AntonDudDm/Hydraulic-manipulator/CAD/Шприц/шприц сборка.SLDASM

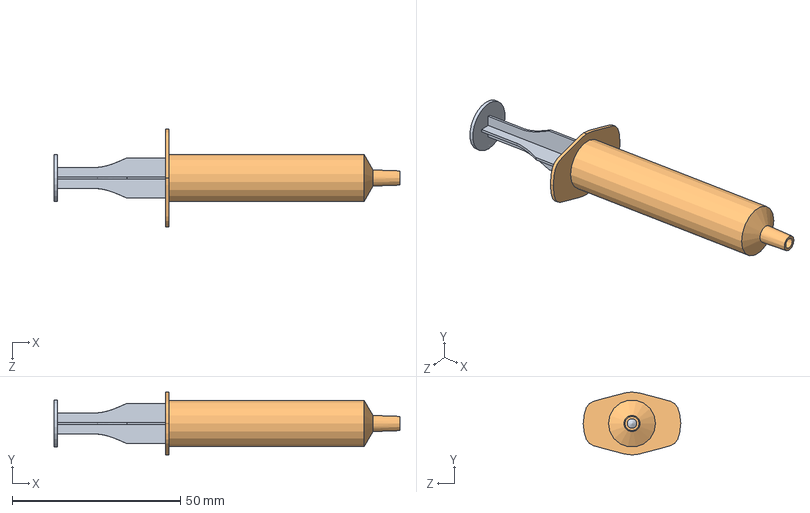
[picture p15: CAD file, 2025-12-12]
CAD/Шприц/шприц сборка.SLDASM
102.8 x 18.7 x 29.0 mm
шприц корпус 5 мм
шприц шток 5 мм
