AntonDudDm/Hydraulic-manipulator/CAD/Захват и мотор №4/Шарнир наклона захвата/Шарнир захвата.SLDPRT

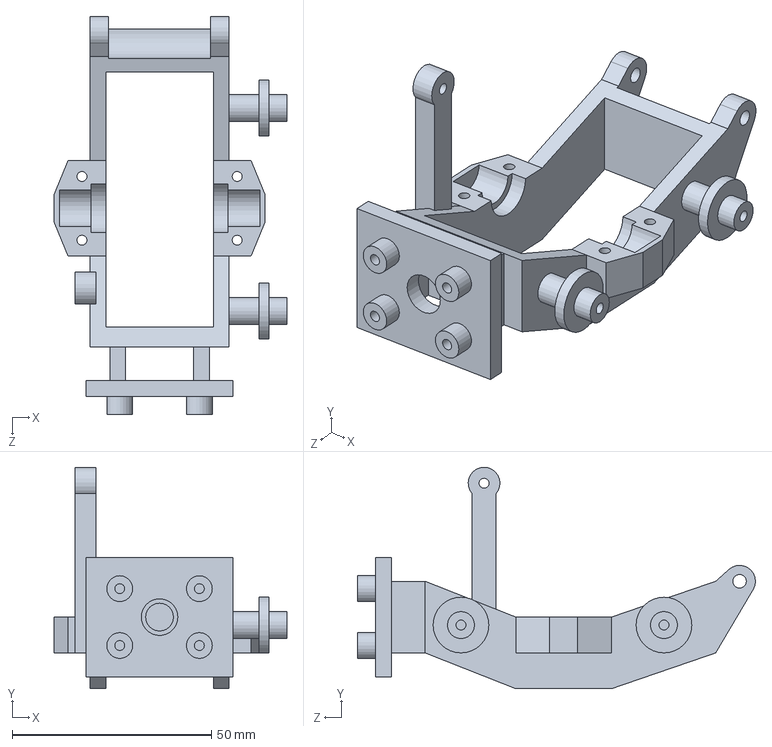
[picture p22: CAD file, 2025-12-12]
CAD/Захват и мотор №4/Шарнир наклона захвата/Шарнир захвата.SLDPRT
58.5 x 55.6 x 100.0 mm
