AntonDudDm/Hydraulic-manipulator/CAD/Крепежи оси №2/Крепеж подрельсовые к мотору №2 верхняя.SLDPRT

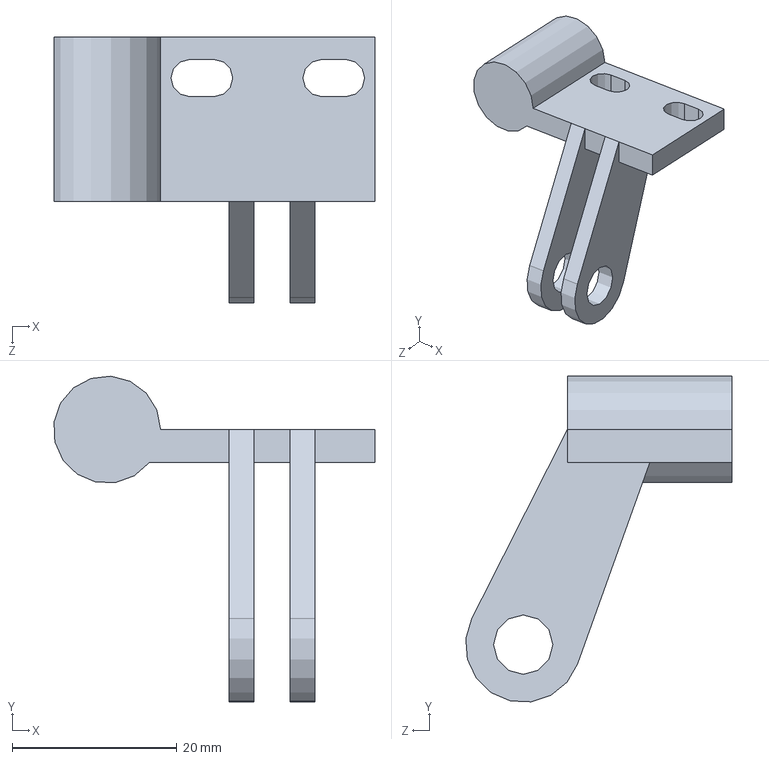
[picture p23: CAD file, 2025-12-12]
CAD/Крепежи оси №2/Крепеж подрельсовые к мотору №2 верхняя.SLDPRT
38.9 x 39.5 x 32.3 mm
