AntonDudDm/Hydraulic-manipulator/CAD/Мотор №1/Детали/Тяга с шайбой_1 ось.SLDPRT

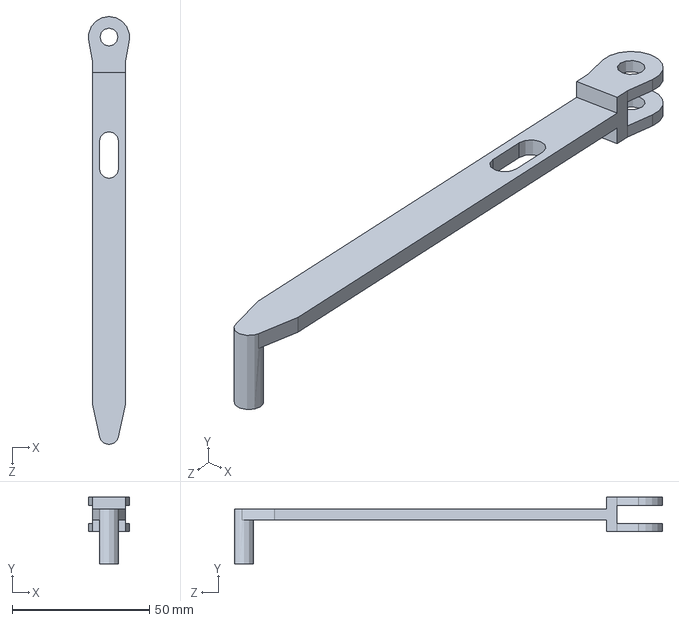
[picture p24: CAD file, 2025-12-12]
CAD/Мотор №1/Детали/Тяга с шайбой_1 ось.SLDPRT
14.8 x 24.2 x 156.0 mm
