AntonDudDm/Hydraulic-manipulator/CAD/Мотор №2/Детали/Заглушка на ось_на клей.SLDPRT

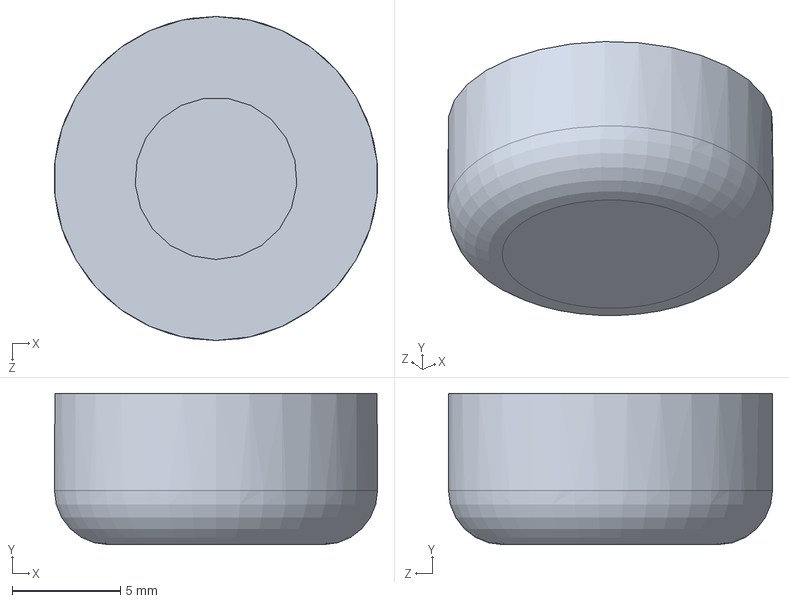
[picture p25: CAD file, 2025-12-12]
CAD/Мотор №2/Детали/Заглушка на ось_на клей.SLDPRT
15.0 x 7.00 x 15.0 mm
