AntonDudDm/Hydraulic-manipulator/CAD/Мотор №3/Детали  мотор №3/Крепёж штока мотора мотор №3.SLDPRT

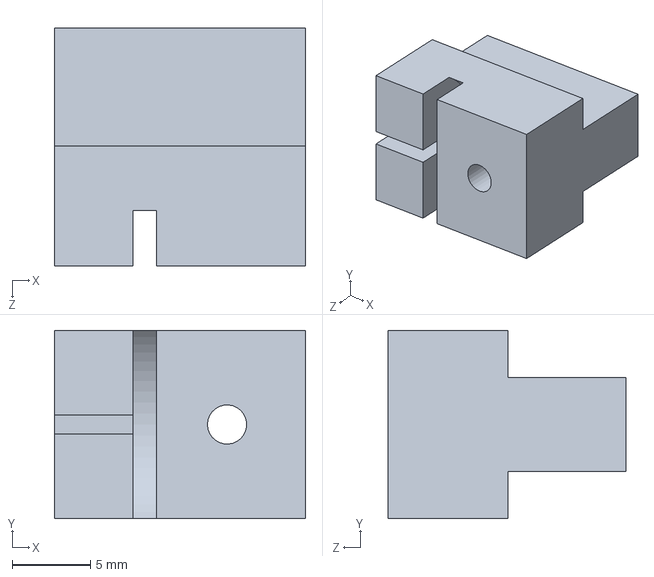
[picture p26: CAD file, 2025-12-12]
CAD/Мотор №3/Детали мотор №3/Крепёж штока мотора мотор №3.SLDPRT
16.0 x 12.0 x 15.1 mm
