AntonDudDm/Hydraulic-manipulator/CAD/Шприц/шприц корпус 5 мм.SLDPRT

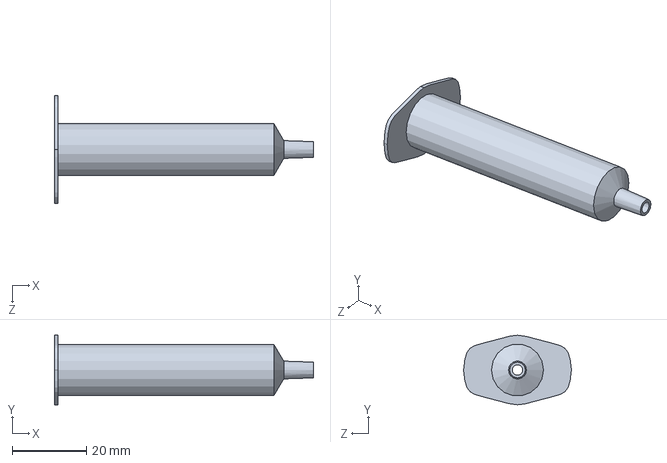
[picture p27: CAD file, 2025-12-12]
CAD/Шприц/шприц корпус 5 мм.SLDPRT
69.7 x 18.7 x 29.0 mm
