AntonDudDm/Hydraulic-manipulator/CAD/Гидронасос/Детали гидронасос/Крепёж к платформе.SLDPRT

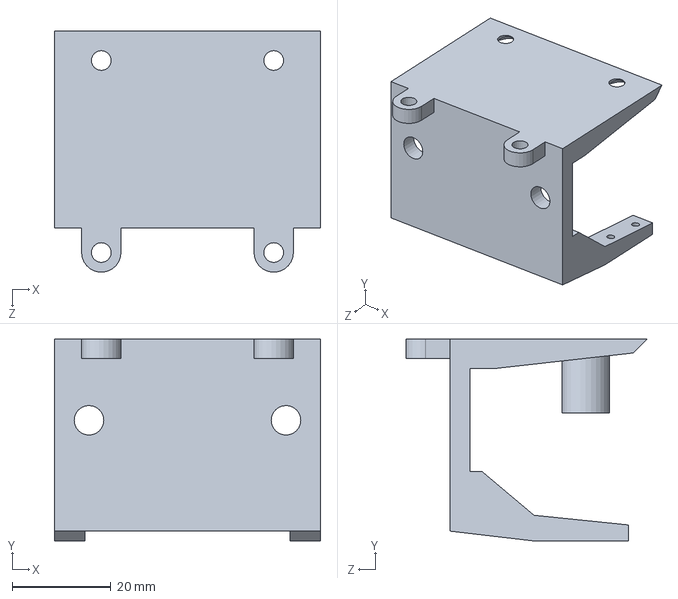
[picture p28: CAD file, 2025-12-12]
CAD/Гидронасос/Детали гидронасос/Крепёж к платформе.SLDPRT
54.0 x 41.0 x 49.0 mm
