AntonDudDm/Hydraulic-manipulator/CAD/Гидронасос/Сервопривод/Прицепная шайба.SLDPRT

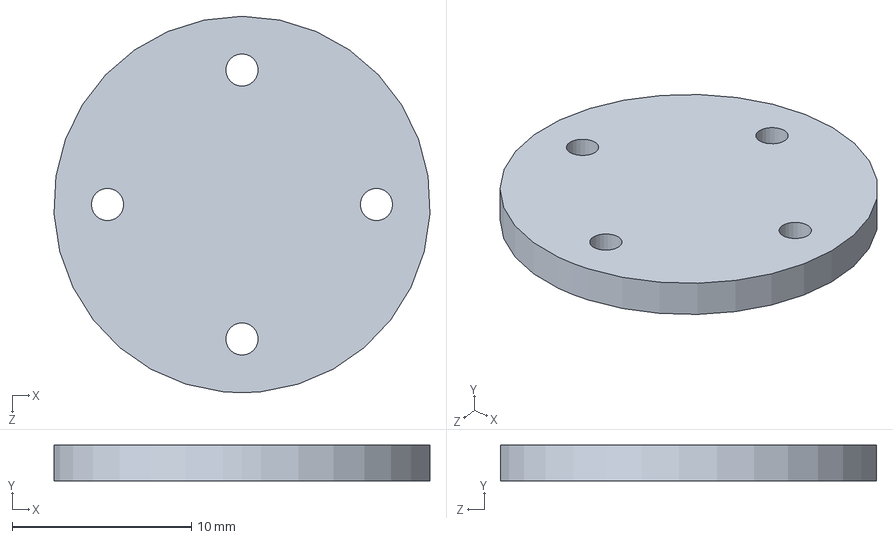
[picture p29: CAD file, 2025-12-12]
CAD/Гидронасос/Сервопривод/Прицепная шайба.SLDPRT
21.0 x 2.00 x 21.0 mm
