AntonDudDm/Hydraulic-manipulator/CAD/Детали и крепления сборки/Крепёж рельсовых.SLDPRT

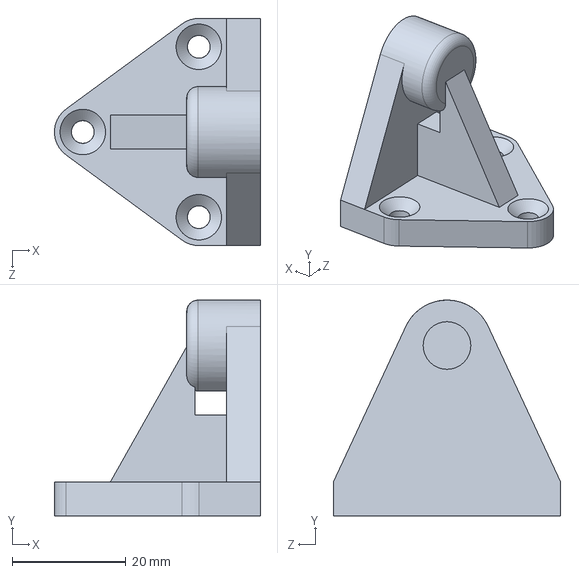
[picture p30: CAD file, 2025-12-12]
CAD/Детали и крепления сборки/Крепёж рельсовых.SLDPRT
36.3 x 38.0 x 40.0 mm
