AntonDudDm/Hydraulic-manipulator/CAD/Детали под электронику/Джойстик/Коробка под джойстик Верх.SLDPRT

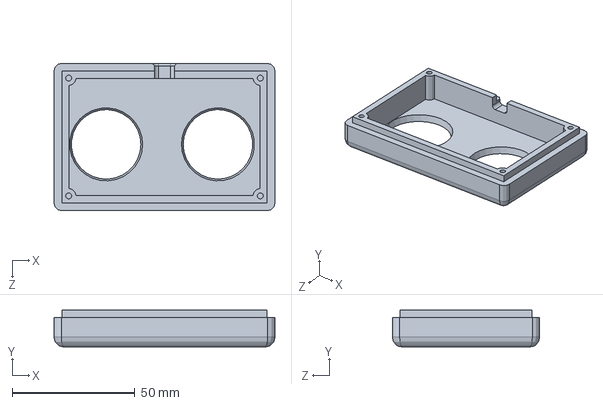
[picture p31: CAD file, 2025-12-12]
CAD/Детали под электронику/Джойстик/Коробка под джойстик Верх.SLDPRT
90.0 x 15.0 x 60.0 mm
