AntonDudDm/Hydraulic-manipulator/CAD/Детали под электронику/крепеж ардуино UNO.SLDPRT

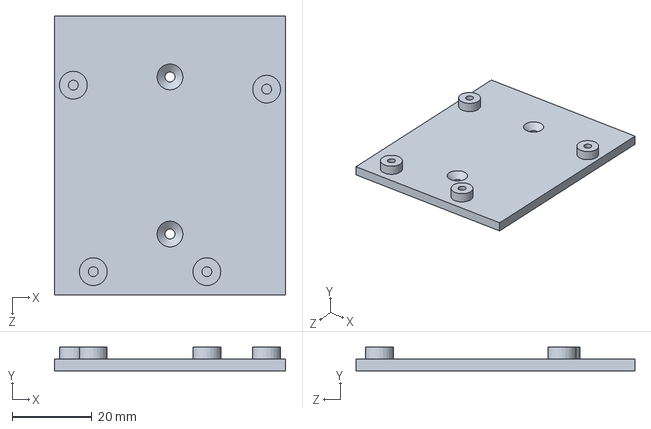
[picture p32: CAD file, 2025-12-12]
CAD/Детали под электронику/крепеж ардуино UNO.SLDPRT
58.0 x 6.00 x 70.0 mm
