AntonDudDm/Hydraulic-manipulator/CAD/Захват и мотор №4/Захват/Детали фаланги/3 фаланга.SLDPRT

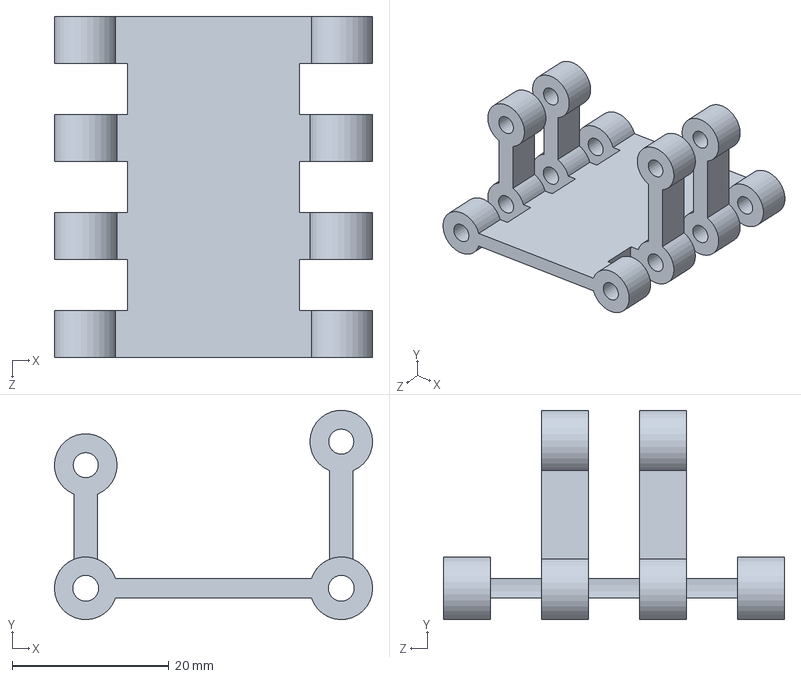
[picture p33: CAD file, 2025-12-12]
CAD/Захват и мотор №4/Захват/Детали фаланги/3 фаланга.SLDPRT
40.6 x 26.7 x 43.5 mm
