AntonDudDm/Hydraulic-manipulator/CAD/Захват и мотор №4/Планетарная передача/Детали планетарка/Сателлит.SLDPRT

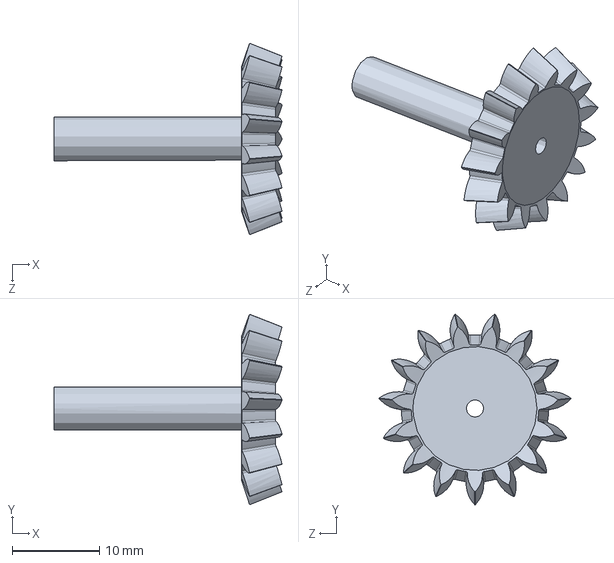
[picture p34: CAD file, 2025-12-12]
CAD/Захват и мотор №4/Планетарная передача/Детали планетарка/Сателлит.SLDPRT
26.2 x 21.9 x 22.0 mm
