AntonDudDm/Hydraulic-manipulator/CAD/Захват и мотор №4/Шток к мотору №3.SLDPRT

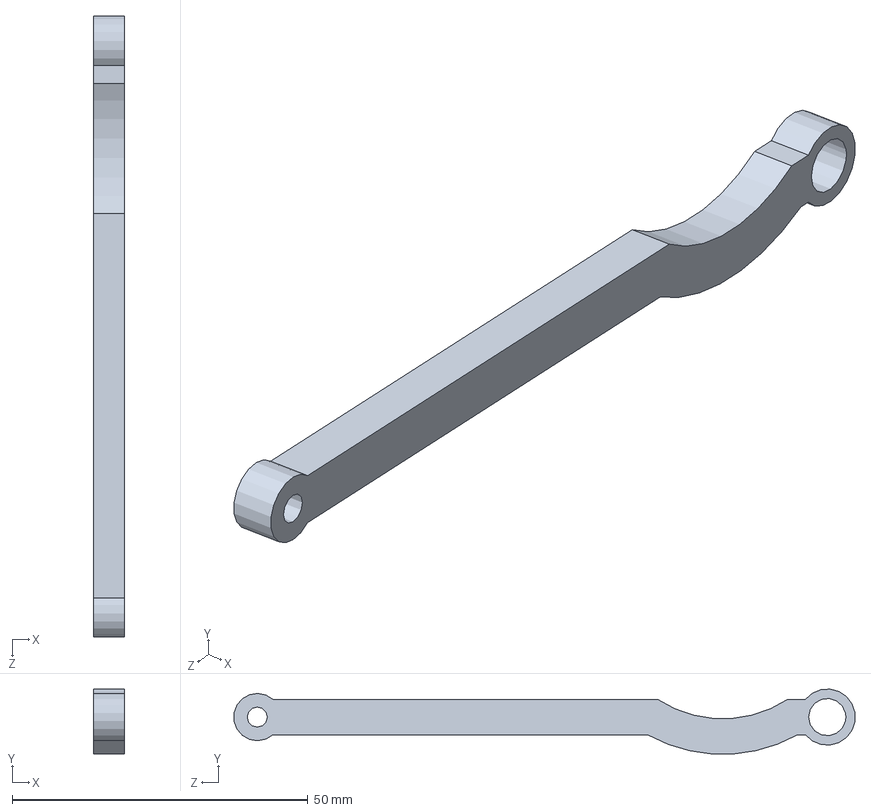
[picture p35: CAD file, 2025-12-12]
CAD/Захват и мотор №4/Шток к мотору №3.SLDPRT
5.20 x 11.0 x 105.0 mm
