AntonDudDm/Hydraulic-manipulator/CAD/Крепежи оси №2/Крепеж подрельсовые к мотору №2 нижняя.SLDPRT

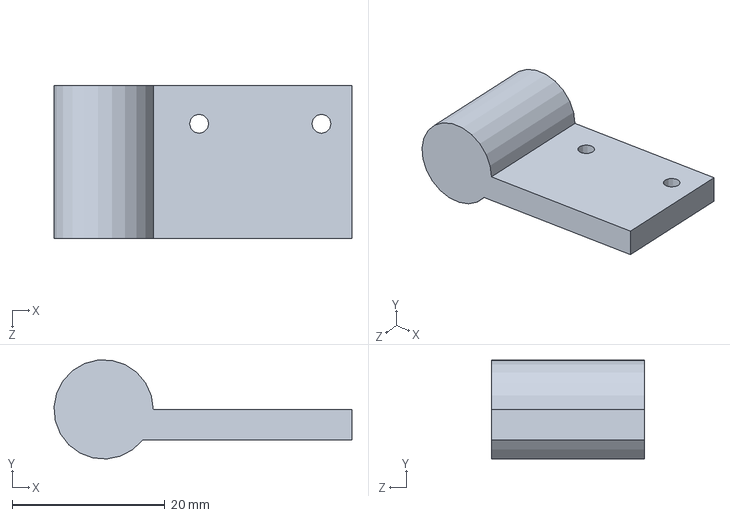
[picture p36: CAD file, 2025-12-12]
CAD/Крепежи оси №2/Крепеж подрельсовые к мотору №2 нижняя.SLDPRT
39.0 x 12.9 x 20.0 mm
