AntonDudDm/Hydraulic-manipulator/CAD/Мотор №1/Детали/Крепёж под шприц_1 ось.SLDPRT

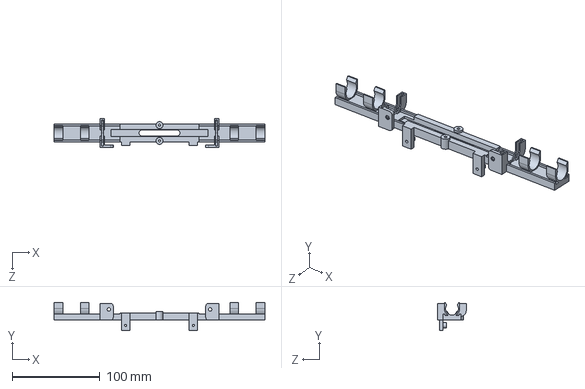
[picture p37: CAD file, 2025-12-12]
CAD/Мотор №1/Детали/Крепёж под шприц_1 ось.SLDPRT
240.0 x 32.2 x 33.0 mm
