AntonDudDm/Hydraulic-manipulator/CAD/Шприц/шприц шток 5 мм.SLDPRT

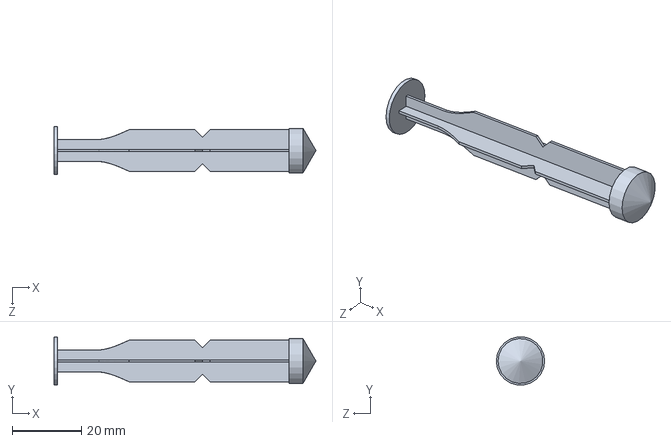
[picture p38: CAD file, 2025-12-12]
CAD/Шприц/шприц шток 5 мм.SLDPRT
75.8 x 13.9 x 14.0 mm
