AntonDudDm/Hydraulic-manipulator/CAD/Гидронасос/Детали гидронасос/Крепёж под шприц, нагнетатель.SLDPRT

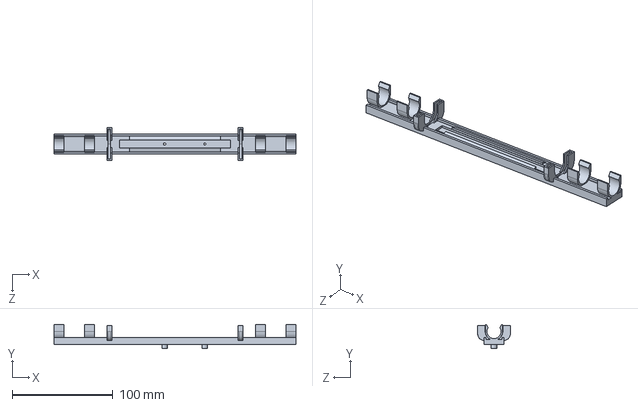
[picture p39: CAD file, 2025-12-12]
CAD/Гидронасос/Детали гидронасос/Крепёж под шприц, нагнетатель.SLDPRT
240.0 x 24.2 x 33.0 mm
