AntonDudDm/Hydraulic-manipulator/CAD/Гидронасос/Сервопривод/Корпус сервопривода.SLDPRT

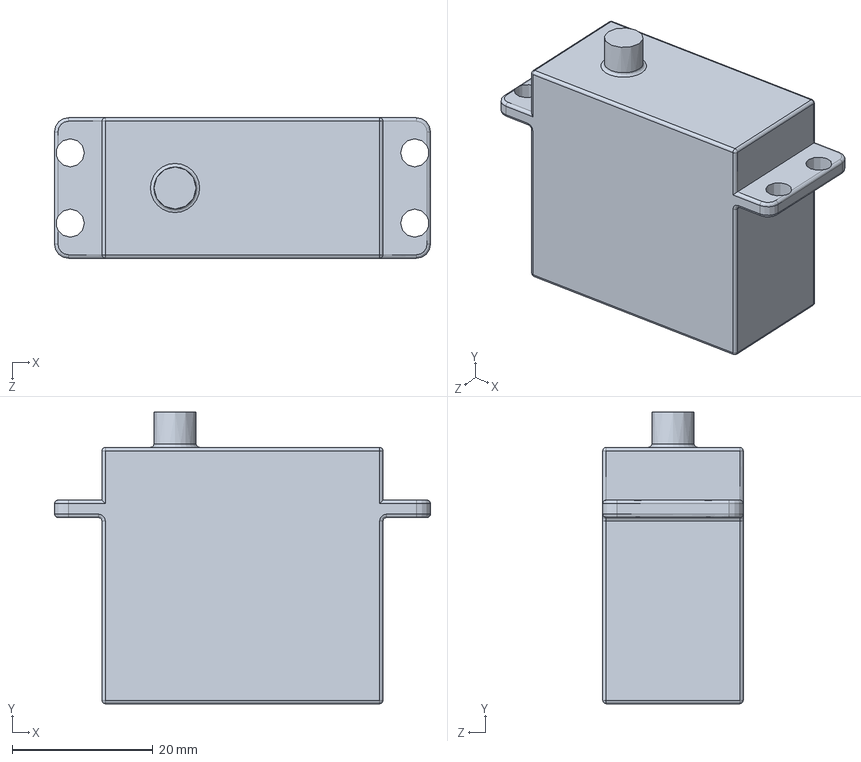
[picture p40: CAD file, 2025-12-12]
CAD/Гидронасос/Сервопривод/Корпус сервопривода.SLDPRT
53.5 x 41.5 x 20.0 mm
