AntonDudDm/Hydraulic-manipulator/CAD/Детали и крепления сборки/стол фанера 18.мм..SLDPRT

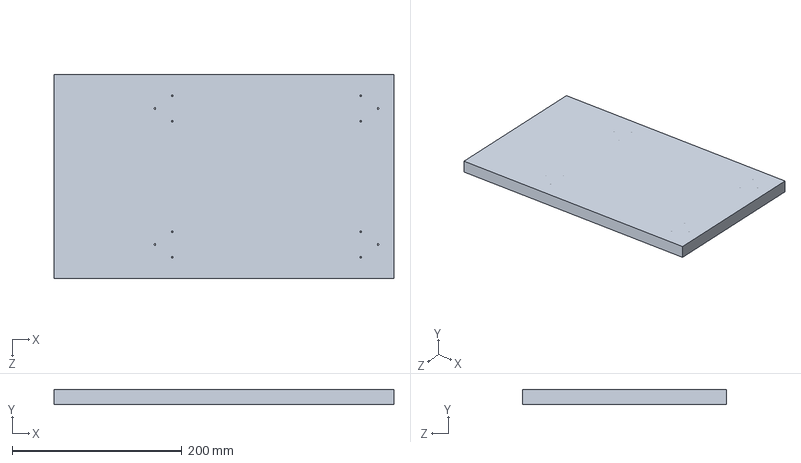
[picture p41: CAD file, 2025-12-12]
CAD/Детали и крепления сборки/стол фанера 18.мм..SLDPRT
400.0 x 18.0 x 240.0 mm
