AntonDudDm/Hydraulic-manipulator/CAD/Детали под электронику/Джойстик/Коробка под джойстик Низ.SLDPRT

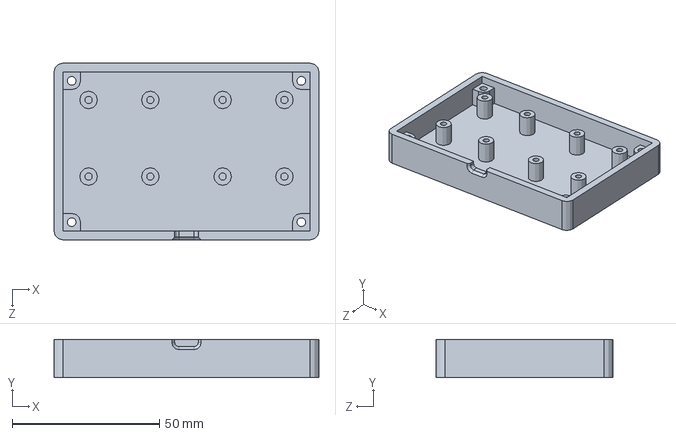
[picture p42: CAD file, 2025-12-12]
CAD/Детали под электронику/Джойстик/Коробка под джойстик Низ.SLDPRT
90.0 x 13.0 x 60.0 mm
