AntonDudDm/Hydraulic-manipulator/CAD/Детали под электронику/Крепеж проводов.SLDPRT

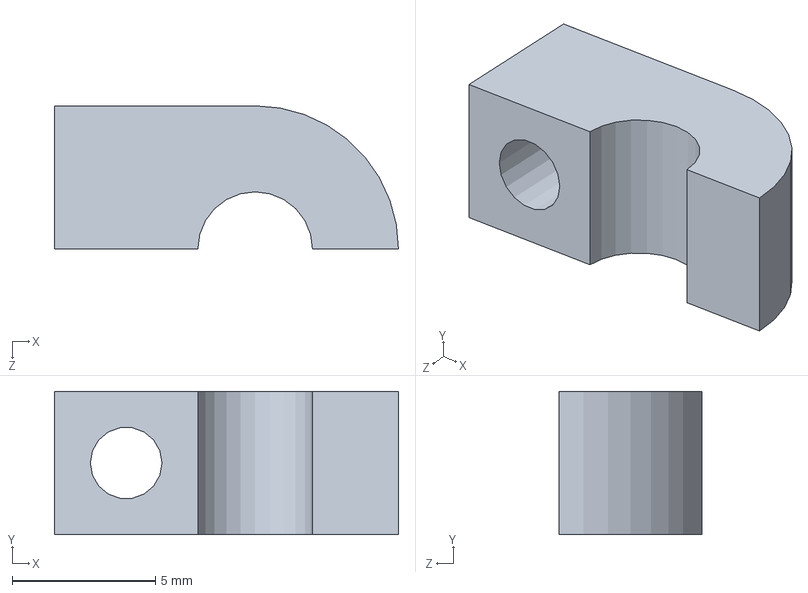
[picture p43: CAD file, 2025-12-12]
CAD/Детали под электронику/Крепеж проводов.SLDPRT
12.0 x 5.00 x 5.00 mm
