AntonDudDm/Hydraulic-manipulator/CAD/Захват и мотор №4/Захват/Детали фаланги/тяга 1 фаланга.SLDPRT

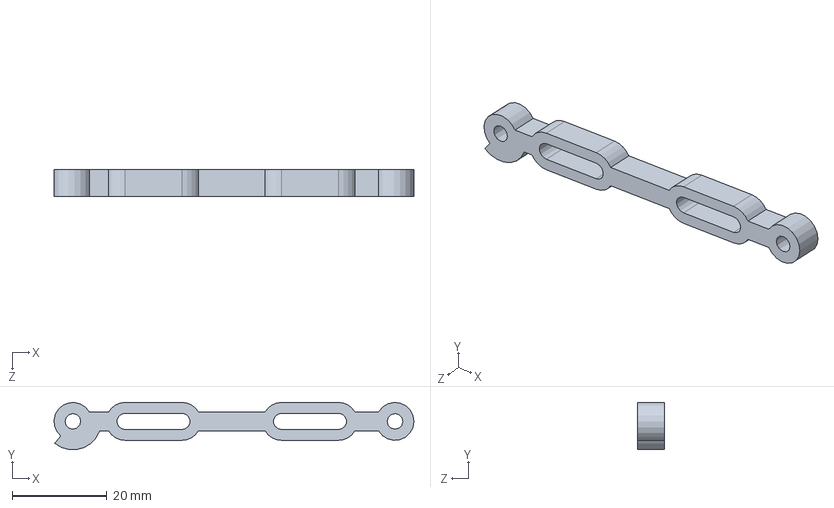
[picture p44: CAD file, 2025-12-12]
CAD/Захват и мотор №4/Захват/Детали фаланги/тяга 1 фаланга.SLDPRT
75.9 x 9.95 x 5.60 mm
