AntonDudDm/Hydraulic-manipulator/CAD/Крепежи оси №2/Крепеж подрельсовые оси №2 к каретке каркаса.SLDPRT

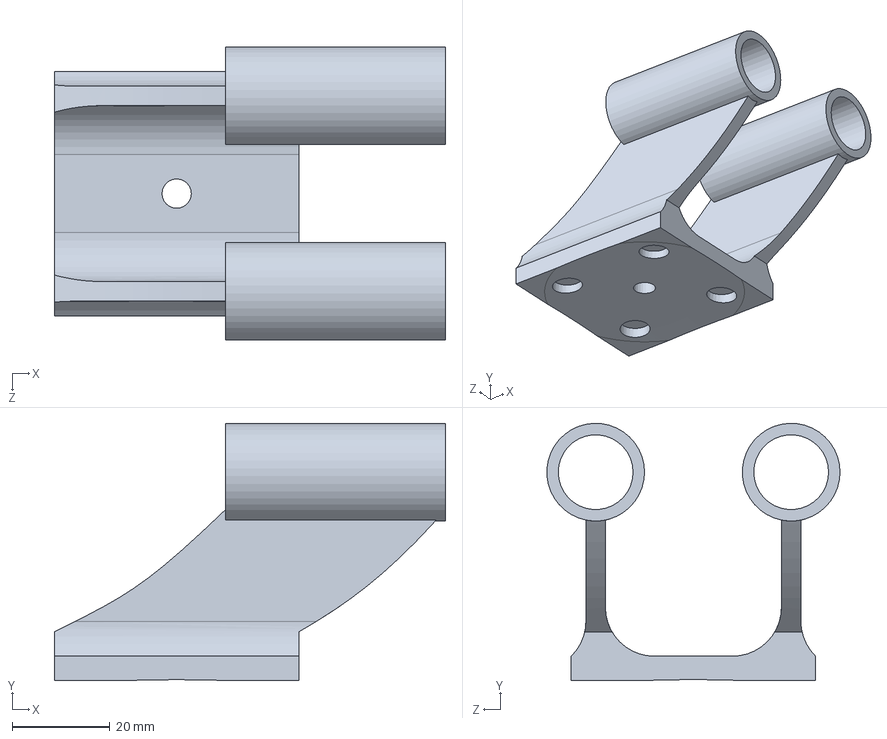
[picture p45: CAD file, 2025-12-12]
CAD/Крепежи оси №2/Крепеж подрельсовые оси №2 к каретке каркаса.SLDPRT
80.0 x 52.6 x 60.0 mm
