AntonDudDm/Hydraulic-manipulator/CAD/Мотор №1/Детали/Крепёж штока_1 ось.SLDPRT

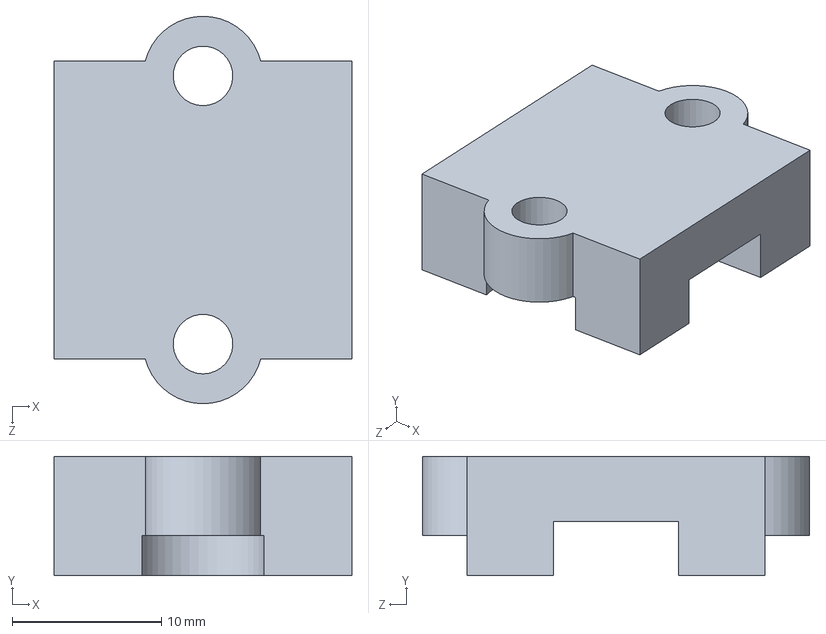
[picture p46: CAD file, 2025-12-12]
CAD/Мотор №1/Детали/Крепёж штока_1 ось.SLDPRT
20.0 x 8.00 x 26.0 mm
