AntonDudDm/Hydraulic-manipulator/CAD/Гидронасос/Детали гидронасос/Рейка на гидронасос.SLDPRT

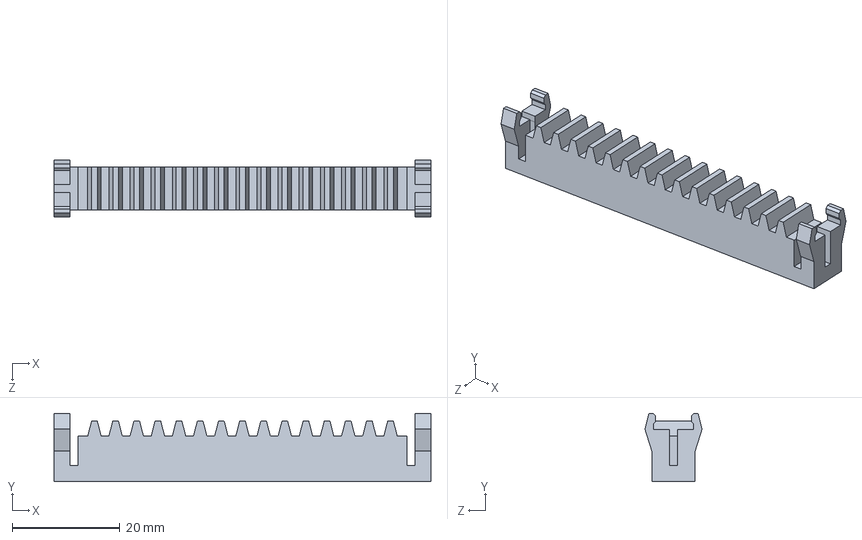
[picture p47: CAD file, 2025-12-12]
CAD/Гидронасос/Детали гидронасос/Рейка на гидронасос.SLDPRT
70.0 x 12.6 x 10.6 mm
