AntonDudDm/Hydraulic-manipulator/CAD/Детали и крепления сборки/Несущая каретка.SLDPRT

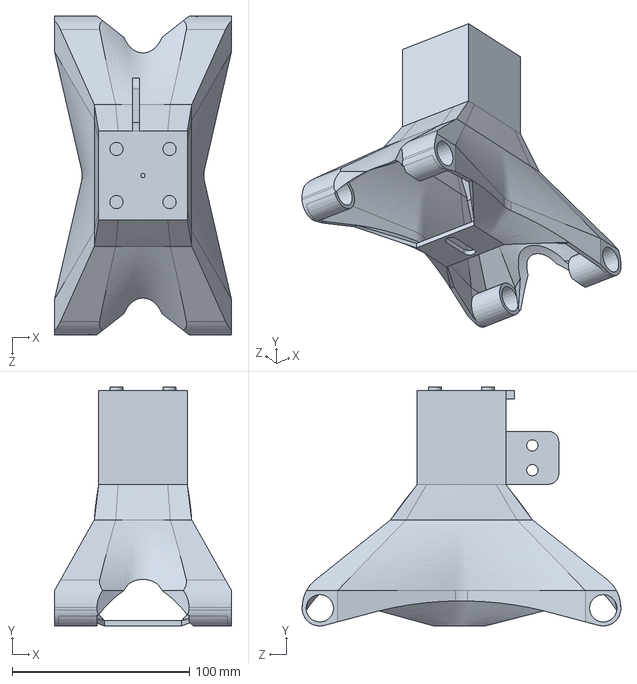
[picture p48: CAD file, 2025-12-12]
CAD/Детали и крепления сборки/Несущая каретка.SLDPRT
100.0 x 135.0 x 180.0 mm
