AntonDudDm/Hydraulic-manipulator/CAD/Детали под электронику/слайсер под аккумулятор.SLDPRT

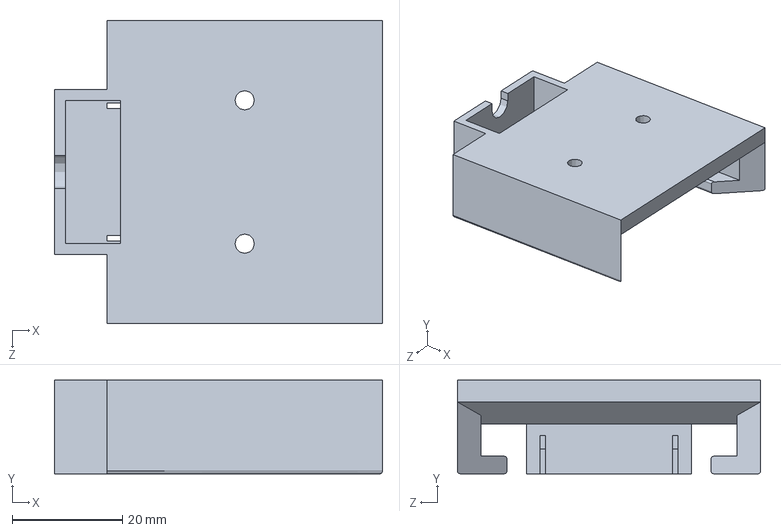
[picture p49: CAD file, 2025-12-12]
CAD/Детали под электронику/слайсер под аккумулятор.SLDPRT
59.5 x 17.0 x 55.0 mm
