AntonDudDm/Hydraulic-manipulator/CAD/Захват и мотор №4/Захват/Детали фаланги/тяга 3 фаланга.SLDPRT

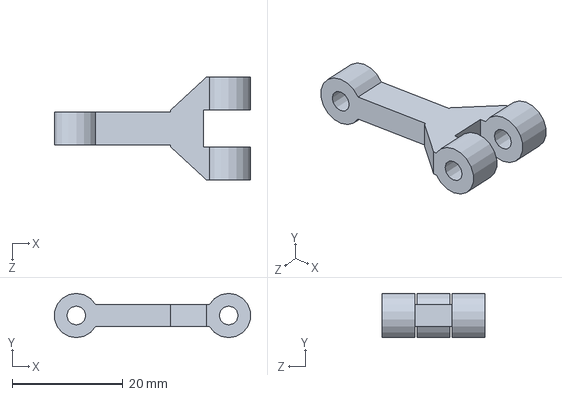
[picture p50: CAD file, 2025-12-12]
CAD/Захват и мотор №4/Захват/Детали фаланги/тяга 3 фаланга.SLDPRT
35.4 x 8.00 x 18.6 mm
