AntonDudDm/Hydraulic-manipulator/CAD/Крепежи оси №2/Крепеж подрельсовые к захвату нижняя.SLDPRT

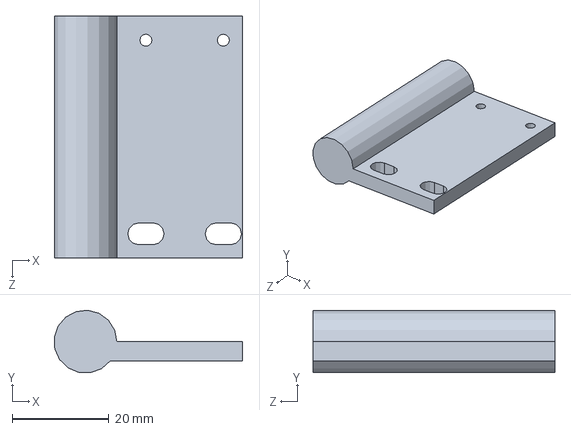
[picture p51: CAD file, 2025-12-12]
CAD/Крепежи оси №2/Крепеж подрельсовые к захвату нижняя.SLDPRT
38.9 x 12.9 x 50.0 mm
