AntonDudDm/Hydraulic-manipulator/CAD/Мотор №1/Детали/Подставка под рычаг_1 ось.SLDPRT

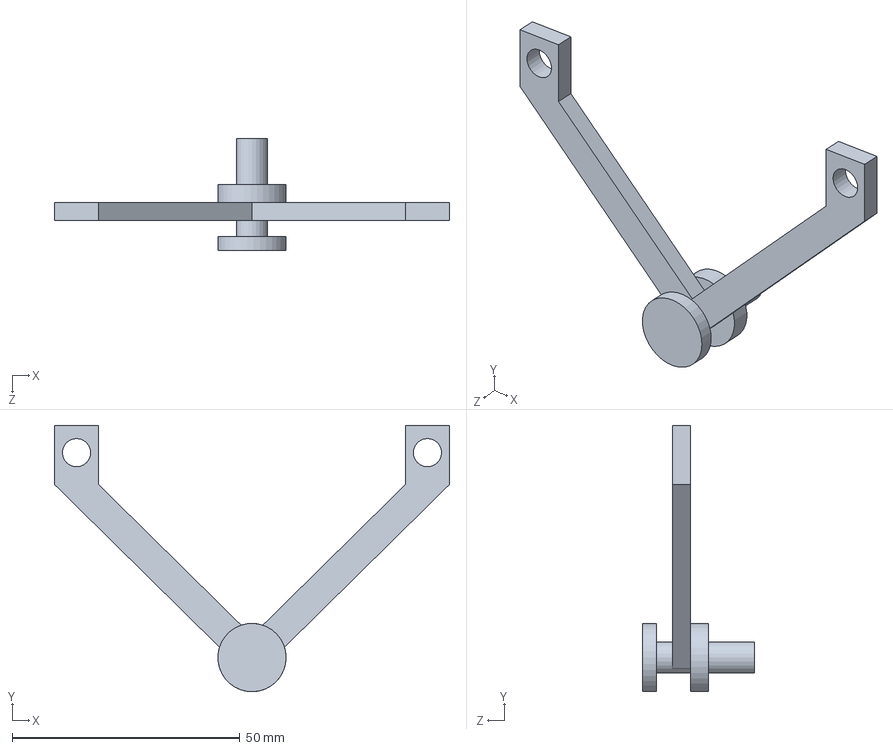
[picture p52: CAD file, 2025-12-12]
CAD/Мотор №1/Детали/Подставка под рычаг_1 ось.SLDPRT
86.8 x 58.5 x 24.5 mm
