AntonDudDm/Hydraulic-manipulator/CAD/Мотор №2/Детали/Рычаг от мотора_вторая ось.SLDPRT

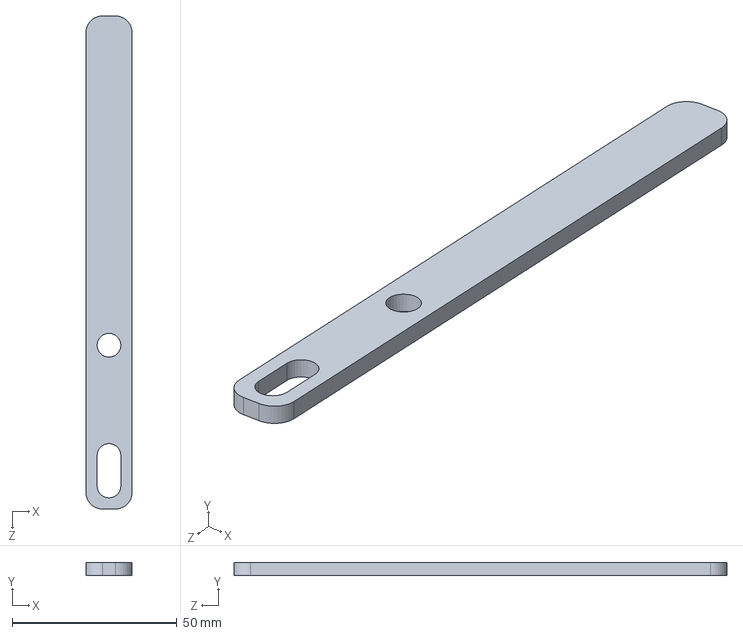
[picture p53: CAD file, 2025-12-12]
CAD/Мотор №2/Детали/Рычаг от мотора_вторая ось.SLDPRT
14.0 x 4.00 x 149.8 mm
