AntonDudDm/Hydraulic-manipulator/CAD/Детали и крепления сборки/Шилдик.SLDPRT

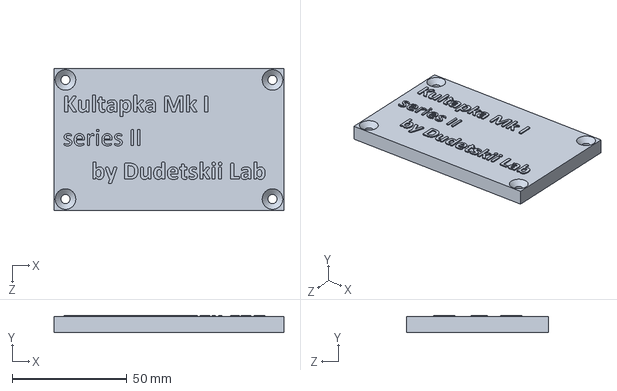
[picture p54: CAD file, 2025-12-12]
CAD/Детали и крепления сборки/Шилдик.SLDPRT
100.0 x 7.50 x 61.8 mm
