AntonDudDm/Hydraulic-manipulator/CAD/Детали под электронику/крепеж под модуль заряа аккумуляторов с BMS.SLDPRT

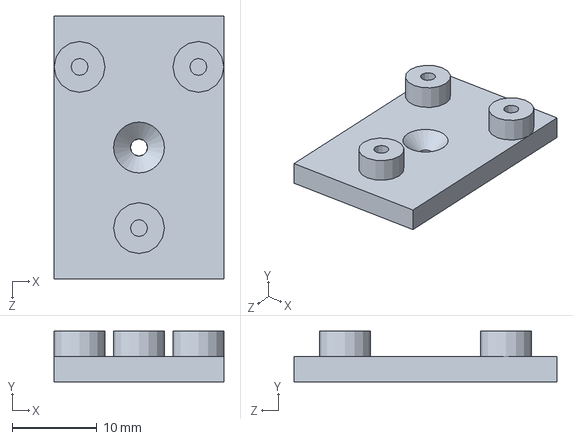
[picture p55: CAD file, 2025-12-12]
CAD/Детали под электронику/крепеж под модуль заряа аккумуляторов с BMS.SLDPRT
20.0 x 6.00 x 31.0 mm
