AntonDudDm/Hydraulic-manipulator/CAD/Захват и мотор №4/Захват/Детали фаланги/тяга 4 фаланга.SLDPRT

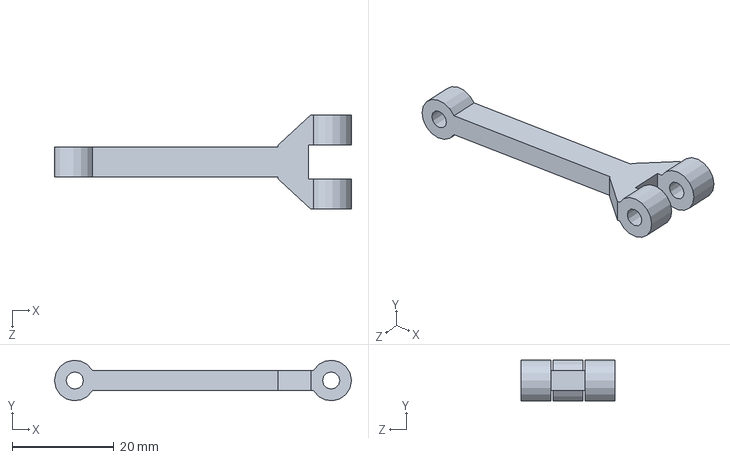
[picture p56: CAD file, 2025-12-12]
CAD/Захват и мотор №4/Захват/Детали фаланги/тяга 4 фаланга.SLDPRT
58.5 x 7.98 x 18.6 mm
