AntonDudDm/Hydraulic-manipulator/CAD/Крепежи оси №2/Подшибник скольжения 8 мм. 15 мм. 45 мм..SLDPRT

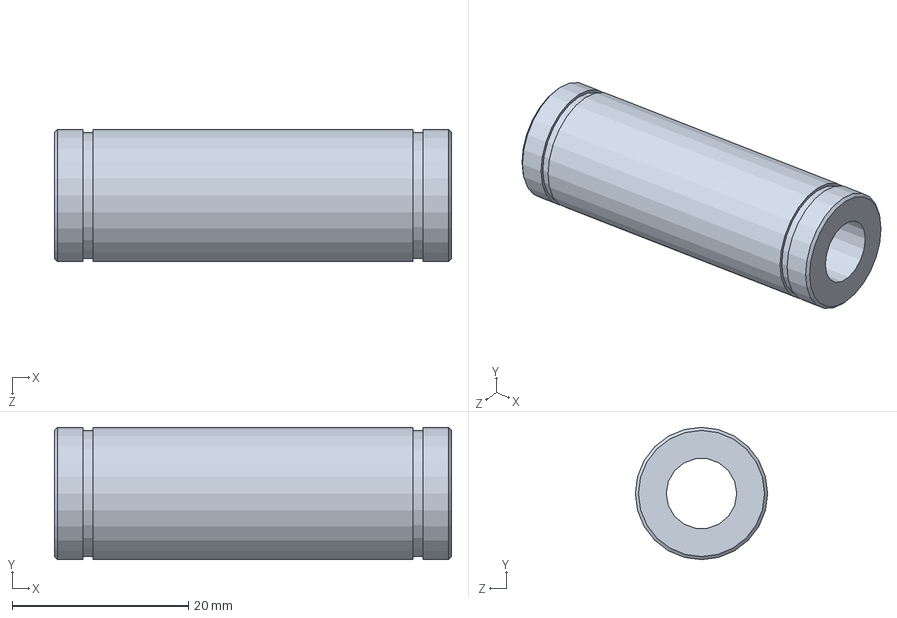
[picture p57: CAD file, 2025-12-12]
CAD/Крепежи оси №2/Подшибник скольжения 8 мм. 15 мм. 45 мм..SLDPRT
45.0 x 15.0 x 15.0 mm
