AntonDudDm/Hydraulic-manipulator/CAD/Мотор №1/Детали/Рейка на гидромотор_1 ось.SLDPRT

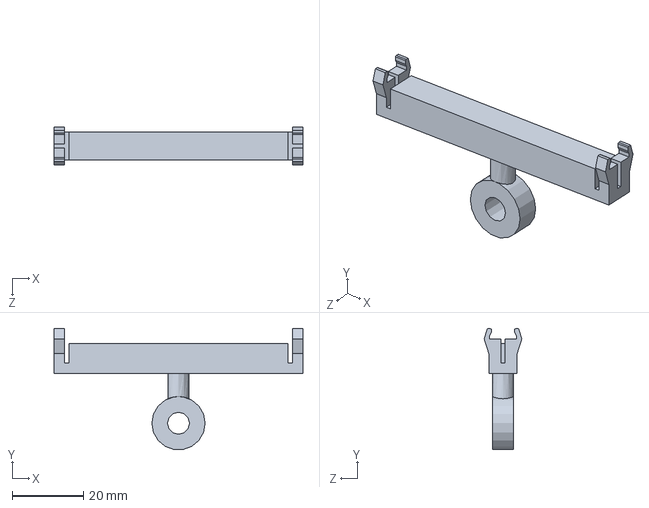
[picture p58: CAD file, 2025-12-12]
CAD/Мотор №1/Детали/Рейка на гидромотор_1 ось.SLDPRT
70.0 x 34.0 x 10.6 mm
