AntonDudDm/Hydraulic-manipulator/CAD/Детали и крепления сборки/Штифт 1 ось свободы.SLDPRT

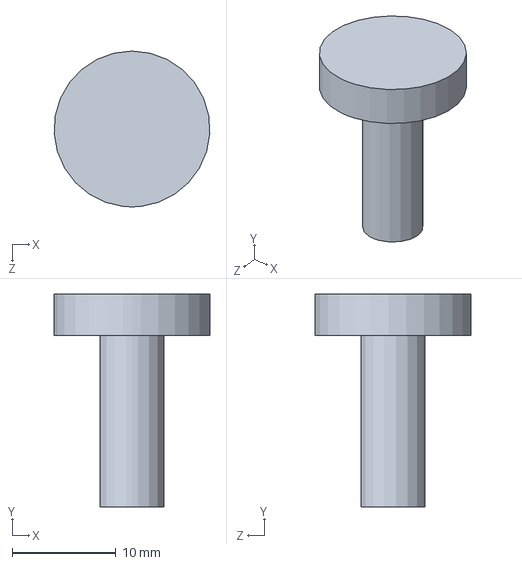
[picture p59: CAD file, 2025-12-12]
CAD/Детали и крепления сборки/Штифт 1 ось свободы.SLDPRT
15.0 x 20.5 x 15.0 mm
