AntonDudDm/Hydraulic-manipulator/CAD/Детали под электронику/Отсек под кнопку.SLDPRT

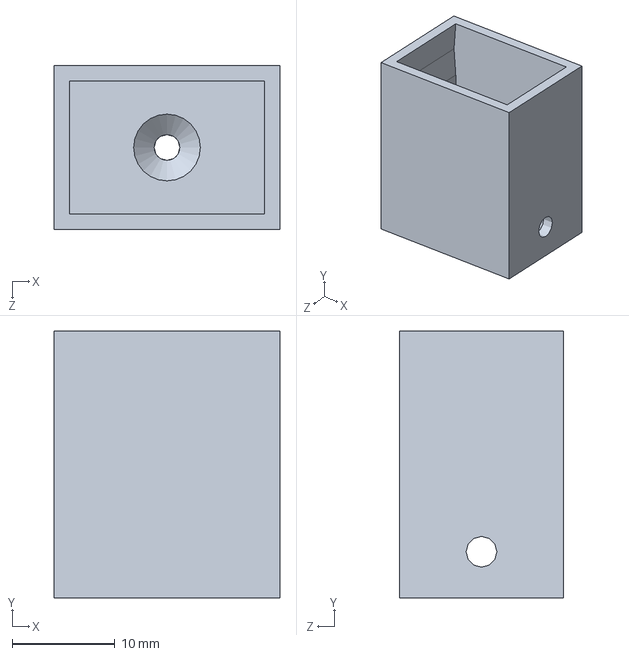
[picture p60: CAD file, 2025-12-12]
CAD/Детали под электронику/Отсек под кнопку.SLDPRT
22.0 x 26.0 x 16.0 mm
