AntonDudDm/Hydraulic-manipulator/CAD/Захват и мотор №4/Захват/Детали фаланги/1 фаланга.SLDPRT

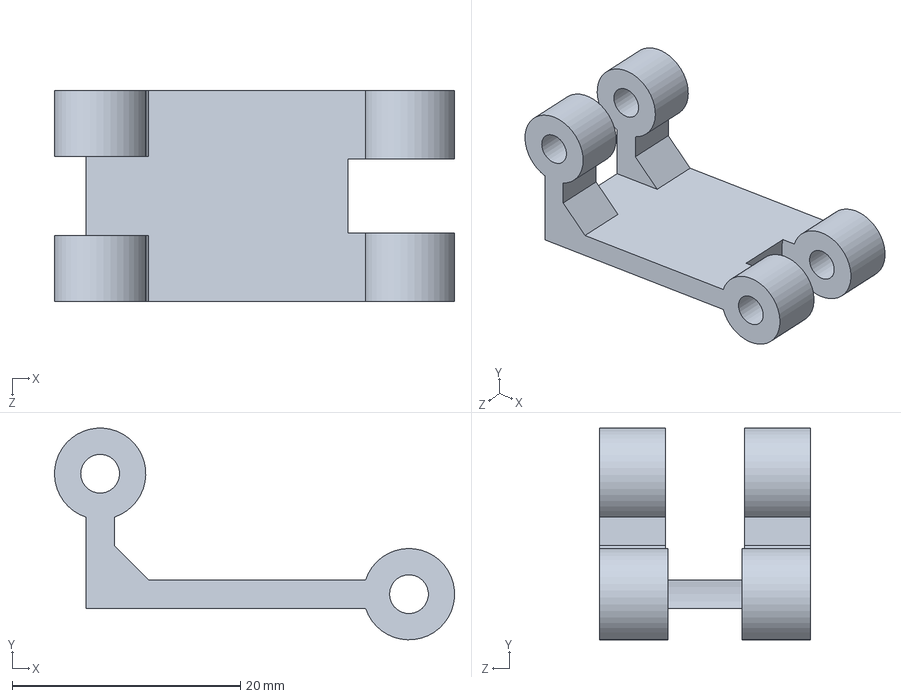
[picture p61: CAD file, 2025-12-12]
CAD/Захват и мотор №4/Захват/Детали фаланги/1 фаланга.SLDPRT
35.0 x 18.5 x 18.5 mm
