AntonDudDm/Hydraulic-manipulator/CAD/Захват и мотор №4/Захват/Детали фаланги/тяга 2 фаланга.SLDPRT

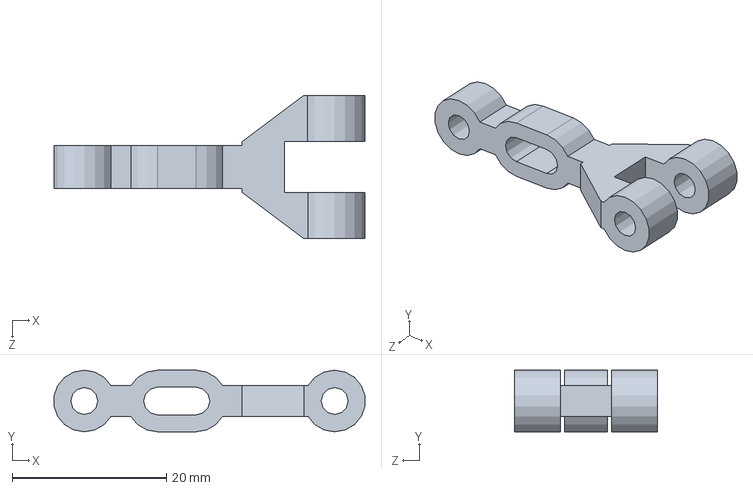
[picture p62: CAD file, 2025-12-12]
CAD/Захват и мотор №4/Захват/Детали фаланги/тяга 2 фаланга.SLDPRT
40.4 x 8.00 x 18.6 mm
