AntonDudDm/Hydraulic-manipulator/CAD/Детали и крепления сборки/Рельсовая прут 8 мм. 220 мм..SLDPRT

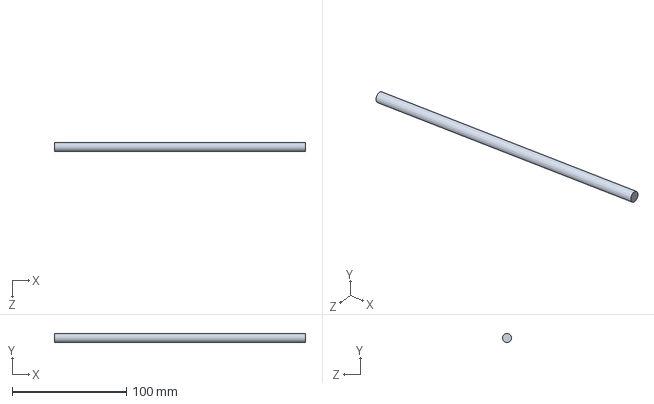
[picture p63: CAD file, 2025-12-12]
CAD/Детали и крепления сборки/Рельсовая прут 8 мм. 220 мм..SLDPRT
220.0 x 8.00 x 8.00 mm
