AntonDudDm/Hydraulic-manipulator/CAD/Мотор №2/Мотор №2 сборка.SLDASM

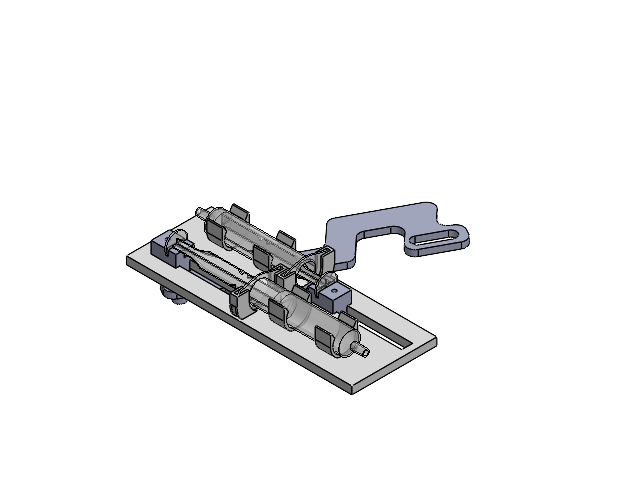
[picture p71: CAD file, 2025-12-12]
CAD/Мотор №2/Мотор №2 сборка.SLDASM
крепёж под шприц мотор 1
шприц корпус 5 мм x 2
шприц шток 5 мм x 2
крепёж штока мотора 1 x 2
подвижный элемент
рычаг на мотор 1
заглушка на клей
