AntonDudDm/Hydraulic-manipulator/CAD/Мотор №3/Мотор №3 сборка.SLDASM

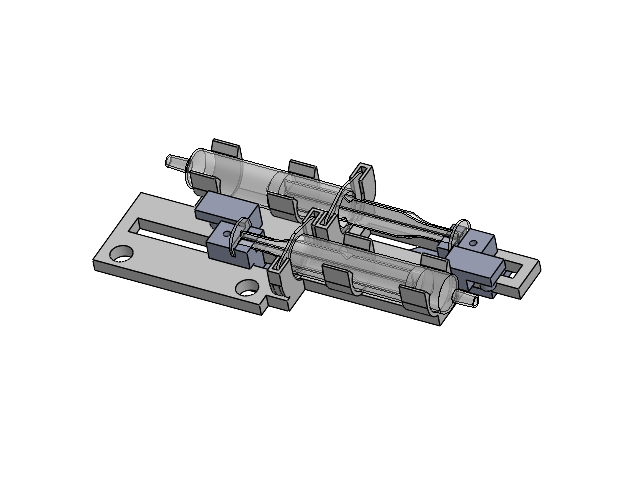
[picture p72: CAD file, 2025-12-12]
CAD/Мотор №3/Мотор №3 сборка.SLDASM
крепёж под шприц мотор 3
крепёж штока мотора 3 x 2
подвижный элемент3
шприц корпус 5 мм x 2
шприц шток 5 мм x 2
