AntonDudDm/Hydraulic-manipulator/CAD/Сборка Манипулятора.SLDASM

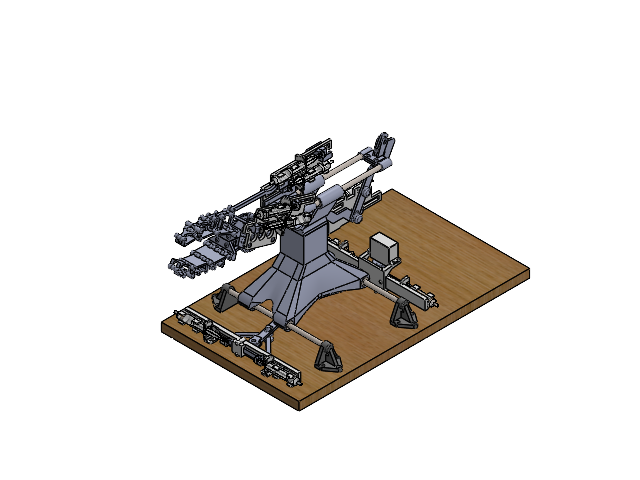
[picture p73: CAD file, 2025-12-12]
CAD/Сборка Манипулятора.SLDASM
стол фанера 18.мм.
крепёж рельсовых x 4
рельсовая прут 8 мм.220 мм. x 4
подшибник скольжения 8 мм. 15 мм. 24 мм. x 4
подвижная коретка квадрат
выдвижная хрень1
подшибник скольжения 8 мм. 15 мм. 45 мм. x 2
крепёж под шприц, нагнетатель
рейка на гидронасос
шприц корпус 5 мм x 10
шприц шток 5 мм x 10
звездочка
корпус
прицепная шайба
крепёж к столу
крепёж под шприц, мотор
рейка на гидромотор
подставка под рычаг
тяга с шайбой
крепёж штока
крепёж под шприц мотор 1
крепёж штока мотора 1 x 2
подвижный элемент
рычаг на мотор 1
заглушка на клей x 2
крепеж подрельсовые 2 выдвижение
крепеж подрельсовые 1 выдвижение
крепеж подрельсовые 3 выдвижение
крепеж подрельсовые 4 выдвижение
крепёж под шприц мотор 3
крепёж штока мотора 3 x 2
подвижный элемент3
шток под руку
крепёж шарнира
шарнир на руку 2
планетарка 1 x 2
сателит 1
тяга на мотор
крепёж под шприц мотор 4
крепёж штока мотора 4 x 2
подвижный элемент4
начало x 2
1 фаланга верх x 2
2 фаланга верх x 2
3 фаланга верх x 2
тяга 1 фаланга x 2
тяга 2 фаланга x 2
тяга 3 фаланга x 2
тяга 4 фаланга x 2
